MeloCuentan/EstacionPrecalentamiento_70x62/imágenes/FTDI.png

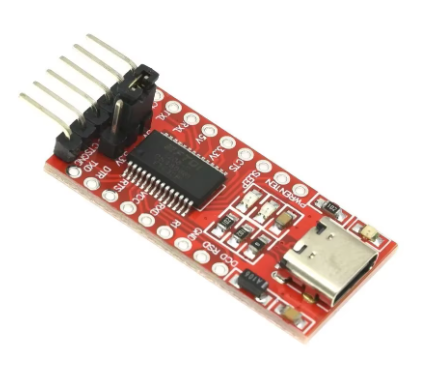
imágenes/FTDI.png
