MeloCuentan/EstacionPrecalentamiento_70x62/imágenes/IMG_20240920_003311_670.jpg

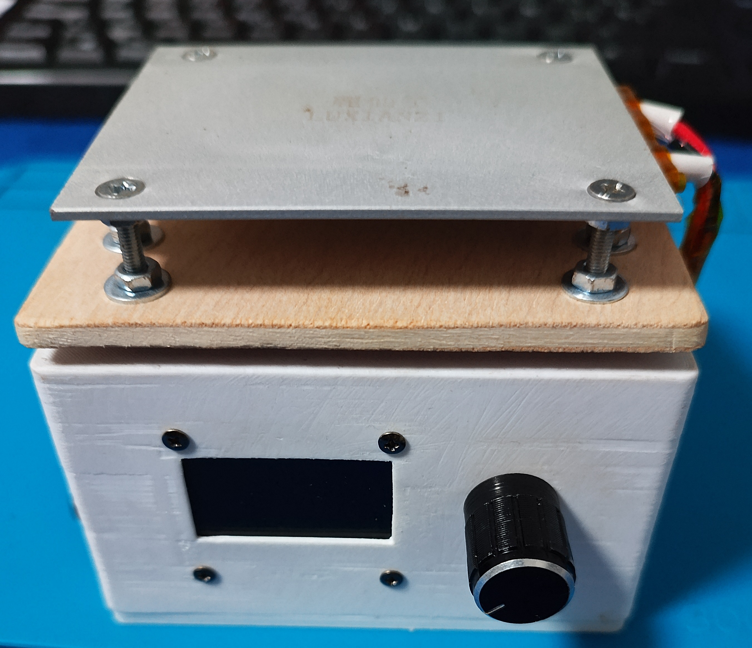
imágenes/IMG_20240920_003311_670.jpg
