MeloCuentan/EstacionPrecalentamiento_70x62/imágenes/IMG_20240920_003321_635.jpg

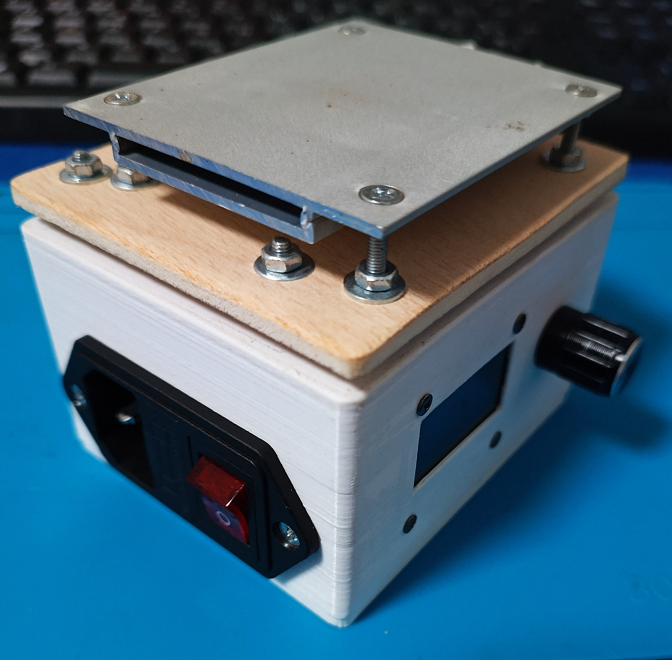
imágenes/IMG_20240920_003321_635.jpg
