MeloCuentan/EstacionPrecalentamiento_70x62/imágenes/LGT8F328P.png

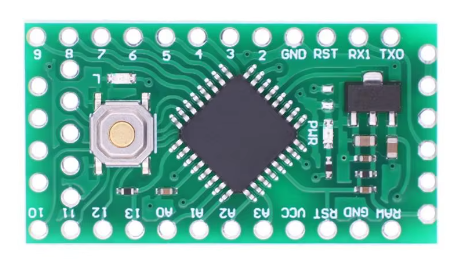
imágenes/LGT8F328P.png
