MeloCuentan/EstacionPrecalentamiento_70x62/imágenes/NTC 100K 3950.png

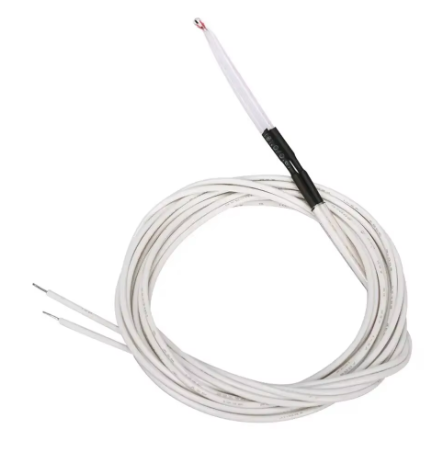
imágenes/NTC 100K 3950.png
