MeloCuentan/EstacionPrecalentamiento_70x62/imágenes/OLED.png

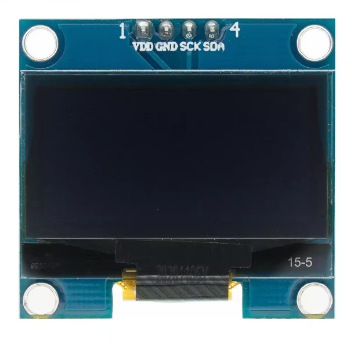
imágenes/OLED.png
