MeloCuentan/EstacionPrecalentamiento_70x62/imágenes/PTC 300W.png

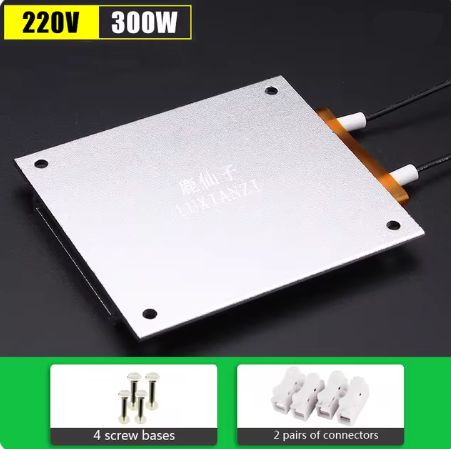
imágenes/PTC 300W.png
